gregminc/8-bit-CPU/Schematics/alu copy.kicad_sch

## KiCad design Schematics/alu copy.kicad_sch (2026-07-09)

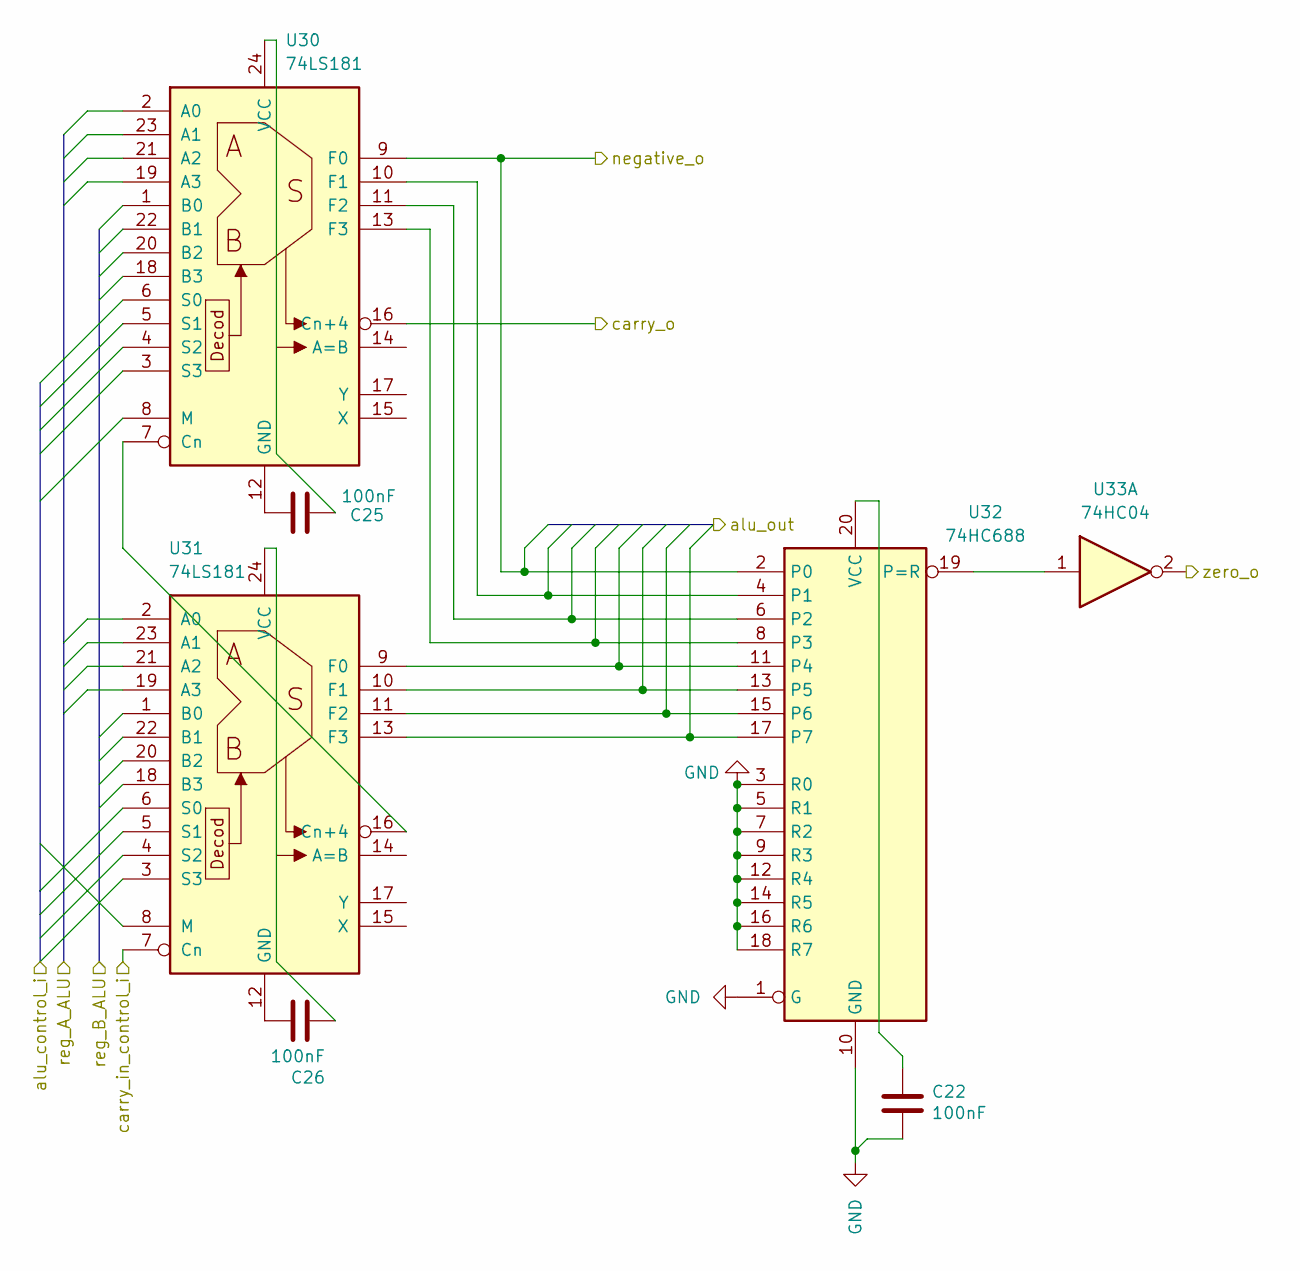
[picture p2: schematic alu copy.kicad_sch]

Parts:
C22, C25, C26: 100nF
U30, U31: 74LS181
U32: 74HC688
U33: 74HC04

Connections:
GND: C22.2, U32.1 (G), U32.3 (R0), U32.5 (R1), U32.7 (R2), U32.9 (R3), U32.10 (GND), U32.12 (R4), U32.14 (R5), U32.16 (R6), U32.18 (R7)
unnamed: C22.1, U32.20 (VCC)
unnamed: C25.1, U30.12 (GND)
unnamed: C25.2, U30.24 (VCC)
unnamed: C26.1, U31.12 (GND)
unnamed: C26.2, U31.24 (VCC)
unnamed: U30.7 (Cn), U31.16 (Cn+4)
unnamed: U30.10 (F1), U32.4 (P1)
unnamed: U30.11 (F2), U32.6 (P2)
unnamed: U30.13 (F3), U32.8 (P3)
unnamed: U31.6 (S0), U31.8 (M)
unnamed: U31.9 (F0), U32.11 (P4)
unnamed: U31.10 (F1), U32.13 (P5)
unnamed: U31.11 (F2), U32.15 (P6)
unnamed: U31.13 (F3), U32.17 (P7)
unnamed: U32.19 (P=R), U33.1
carry_in_control_i: U31.7 (Cn)
carry_o: U30.16 (Cn+4)
negative_o: U30.9 (F0), U32.2 (P0)
zero_o: U33.2
