gregminc/8-bit-CPU/Schematics/clock copy.kicad_sch

## KiCad design Schematics/clock copy.kicad_sch (2026-07-09)

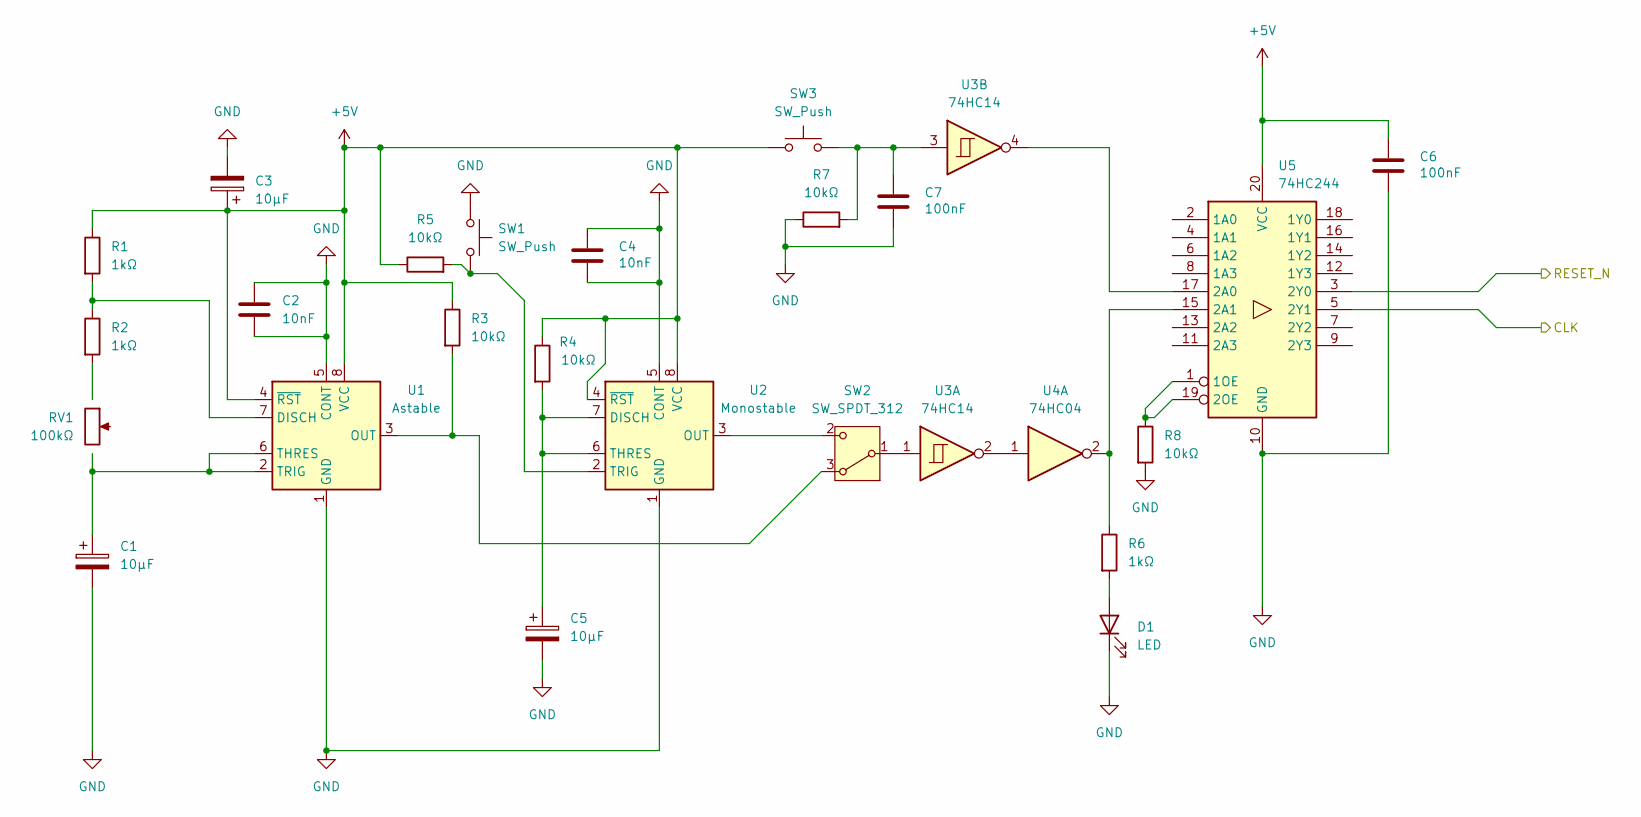
[picture p3: schematic clock copy.kicad_sch]

Parts:
C1, C3, C5: 10µF
C2, C4: 10nF
C6, C7: 100nF
D1: LED
R1, R2, R6: 1kΩ
R3, R4, R5, R7, R8: 10kΩ
RV1: 100kΩ
SW1, SW3: SW_Push
SW2: SW_SPDT_312
U1: Astable; DIP-8_W7.62mm
U2: Monostable; DIP-8_W7.62mm
U3: 74HC14
U4: 74HC04
U5: 74HC244

Connections:
+5V: C3.1, C6.1, R1.1, R3.1, R4.1, R5.1, SW3.1, U1.4 (~RST), U1.8 (VCC), U2.4 (~RST), U2.8 (VCC), U5.20 (VCC)
CLK: U5.5 (2Y1)
GND: C1.2, C2.1, C2.2, C3.2, C4.1, C4.2, C5.2, C6.2, C7.2, D1.1 (K), R7.1, R8.2, SW1.1, U1.1 (GND), U1.5 (CONT), U2.1 (GND), U2.5 (CONT), U5.10 (GND)
unnamed: C1.1, RV1.3, U1.2 (TRIG), U1.6 (THRES)
unnamed: C5.1, R4.2, U2.6 (THRES), U2.7 (DISCH)
unnamed: C7.1, R7.2, SW3.2, U3.3
unnamed: D1.2 (A), R6.2
unnamed: R1.2, R2.1, U1.7 (DISCH)
unnamed: R2.2, RV1.1
unnamed: R3.2, SW2.3 (A), U1.3 (OUT)
unnamed: R5.2, SW1.2, U2.2 (TRIG)
unnamed: R6.1, U4.2, U5.15 (2A1)
unnamed: R8.1, U5.1 (1OE), U5.19 (2OE)
unnamed: SW2.1 (B), U3.1
unnamed: SW2.2 (C), U2.3 (OUT)
unnamed: U3.2, U4.1
unnamed: U3.4, U5.17 (2A0)
RESET_N: U5.3 (2Y0)
