gregminc/8-bit-CPU/Schematics/cu copy.kicad_sch

## KiCad design Schematics/cu copy.kicad_sch (2026-07-09)

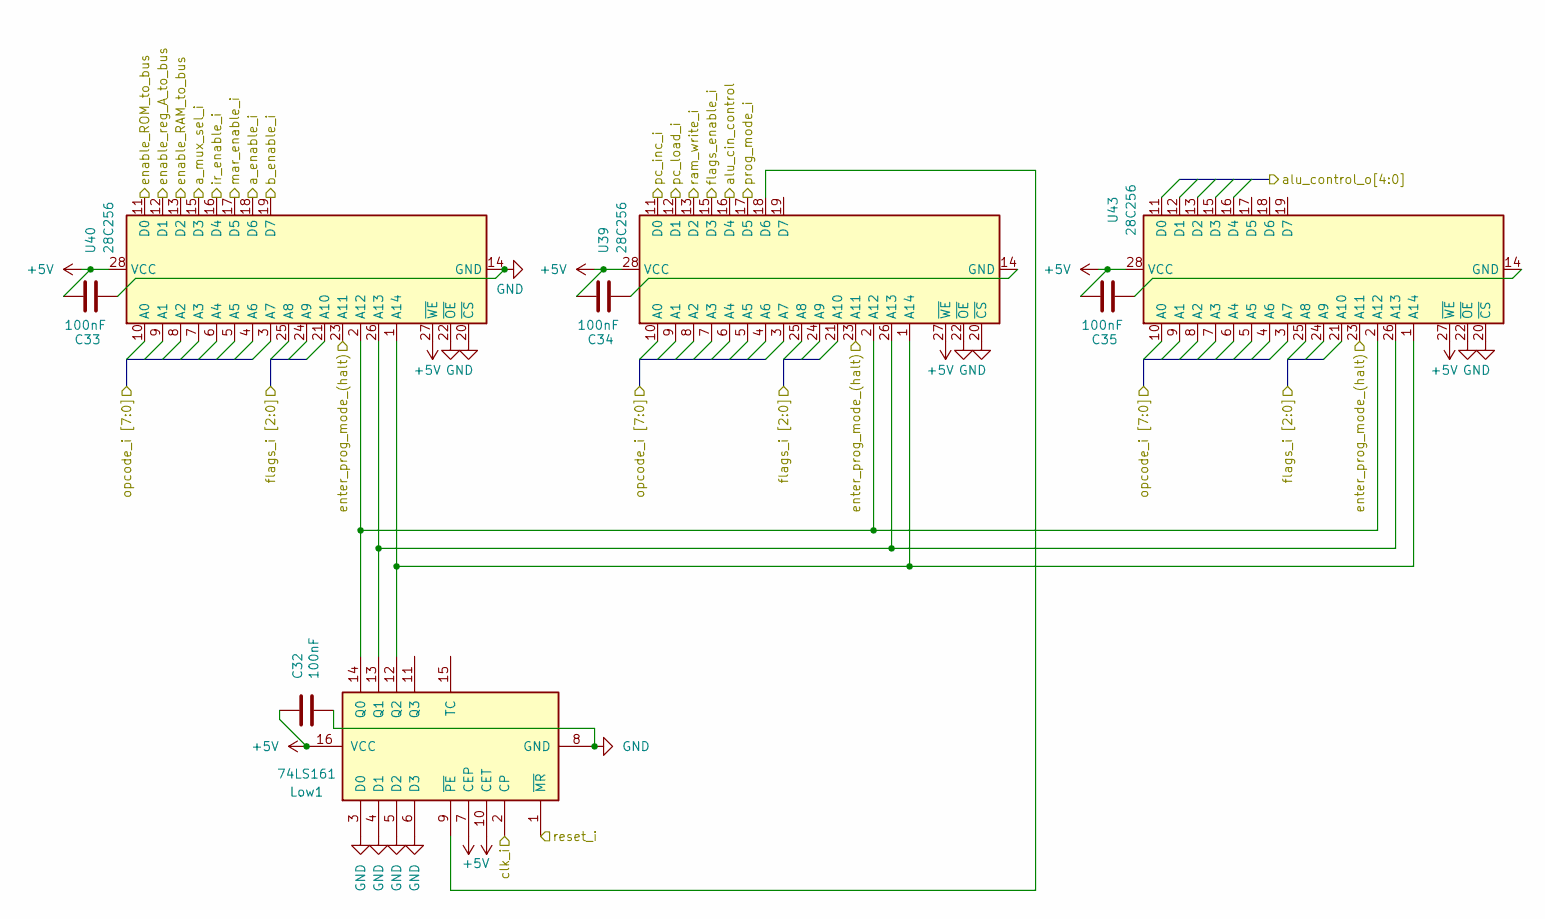
[picture p4: schematic cu copy.kicad_sch]

Parts:
C32, C33, C34, C35: 100nF
Low1: 74LS161
U39, U40, U43: 28C256

Connections:
+5V: C32.1, C33.1, C34.1, C35.1, Low1.7 (CEP), Low1.10 (CET), Low1.16 (VCC), U39.27 (~WE), U39.28 (VCC), U40.27 (~WE), U40.28 (VCC), U43.27 (~WE), U43.28 (VCC)
GND: C32.2, C33.2, Low1.3 (D0), Low1.4 (D1), Low1.5 (D2), Low1.6 (D3), Low1.8 (GND), U39.20 (~CS), U39.22 (~OE), U40.14 (GND), U40.20 (~CS), U40.22 (~OE), U43.20 (~CS), U43.22 (~OE)
unnamed: C34.2, U39.14 (GND)
unnamed: C35.2, U43.14 (GND)
unnamed: Low1.9 (~PE), U39.18 (D6)
unnamed: Low1.12 (Q2), U39.1 (A14), U40.1 (A14), U43.1 (A14)
unnamed: Low1.13 (Q1), U39.26 (A13), U40.26 (A13), U43.26 (A13)
unnamed: Low1.14 (Q0), U39.2 (A12), U40.2 (A12), U43.2 (A12)
a_enable_i: U40.18 (D6)
a_mux_sel_i: U40.15 (D3)
alu_cin_control: U39.16 (D4)
b_enable_i: U40.19 (D7)
clk_i: Low1.2 (CP)
enable_RAM_to_bus: U40.13 (D2)
enable_ROM_to_bus: U40.11 (D0)
enable_reg_A_to_bus: U40.12 (D1)
enter_prog_mode_(halt): U39.23 (A11), U40.23 (A11), U43.23 (A11)
flags_enable_i: U39.15 (D3)
ir_enable_i: U40.16 (D4)
mar_enable_i: U40.17 (D5)
pc_inc_i: U39.11 (D0)
pc_load_i: U39.12 (D1)
prog_mode_i: U39.17 (D5)
ram_write_i: U39.13 (D2)
reset_i: Low1.1 (~MR)
