gregminc/8-bit-CPU/Schematics/flags copy.kicad_sch

## KiCad design Schematics/flags copy.kicad_sch (2026-07-09)

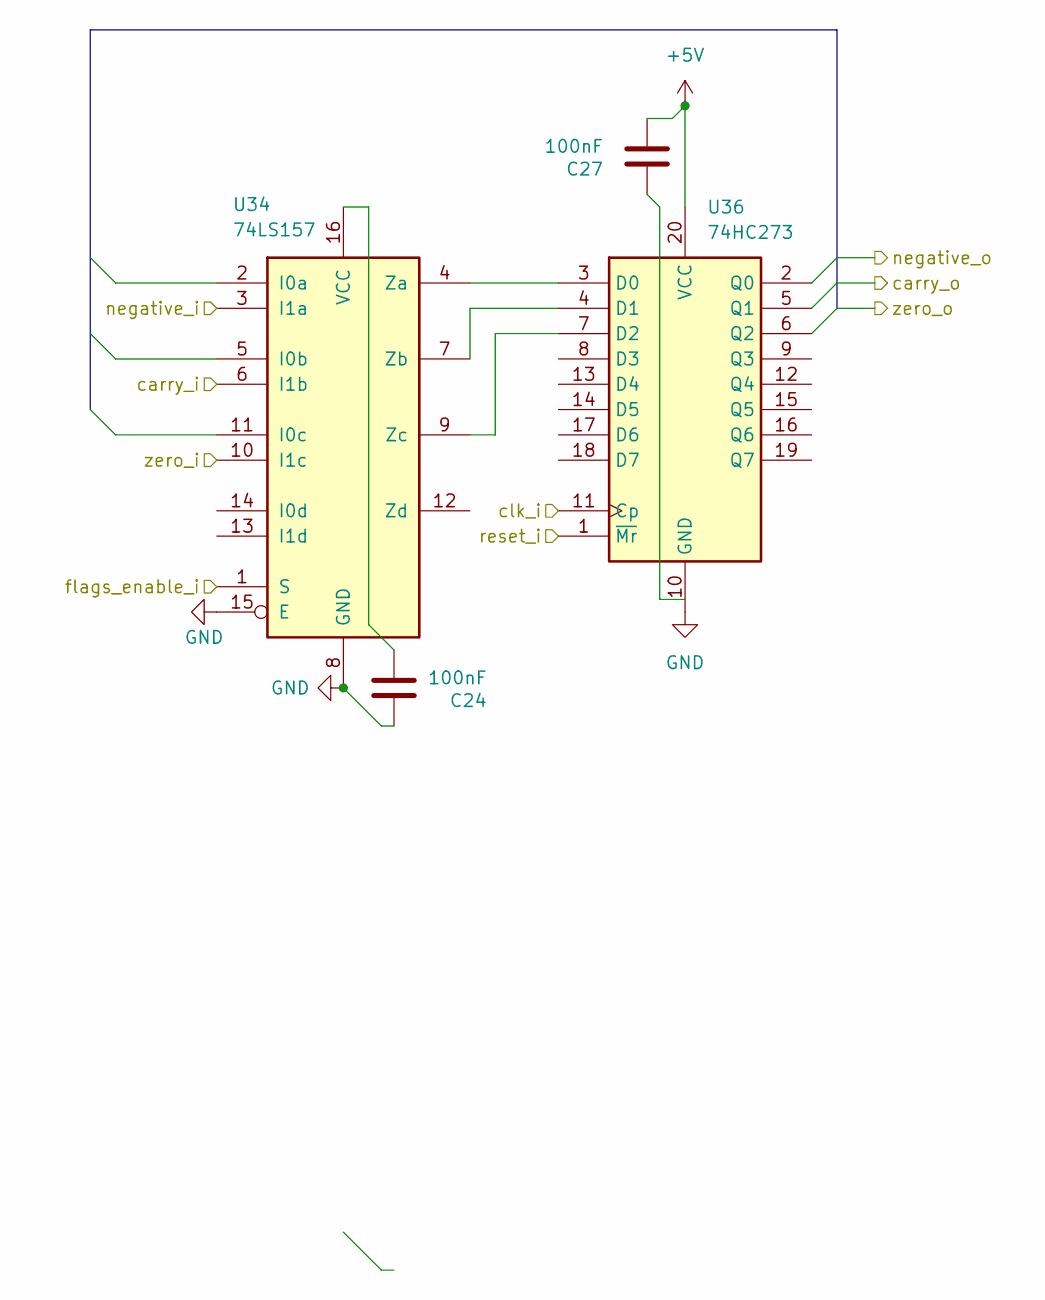
[picture p5: schematic flags copy.kicad_sch]

Parts:
C24, C27: 100nF
U34: 74LS157
U36: 74HC273

Connections:
+5V: C27.2, U36.20 (VCC)
GND: C24.1, U34.8 (GND), U34.15 (E), U36.10 (GND)
unnamed: C24.2, U34.16 (VCC)
unnamed: U34.4 (Za), U36.3 (D0)
unnamed: U34.7 (Zb), U36.4 (D1)
unnamed: U34.9 (Zc), U36.7 (D2)
carry_i: U34.6 (I1b)
clk_i: U36.11 (Cp)
flags_enable_i: U34.1 (S)
negative_i: U34.3 (I1a)
reset_i: U36.1 (~Mr)
zero_i: U34.10 (I1c)
