gregminc/8-bit-CPU/Schematics/io copy.kicad_sch

## KiCad design Schematics/io copy.kicad_sch (2026-07-09)

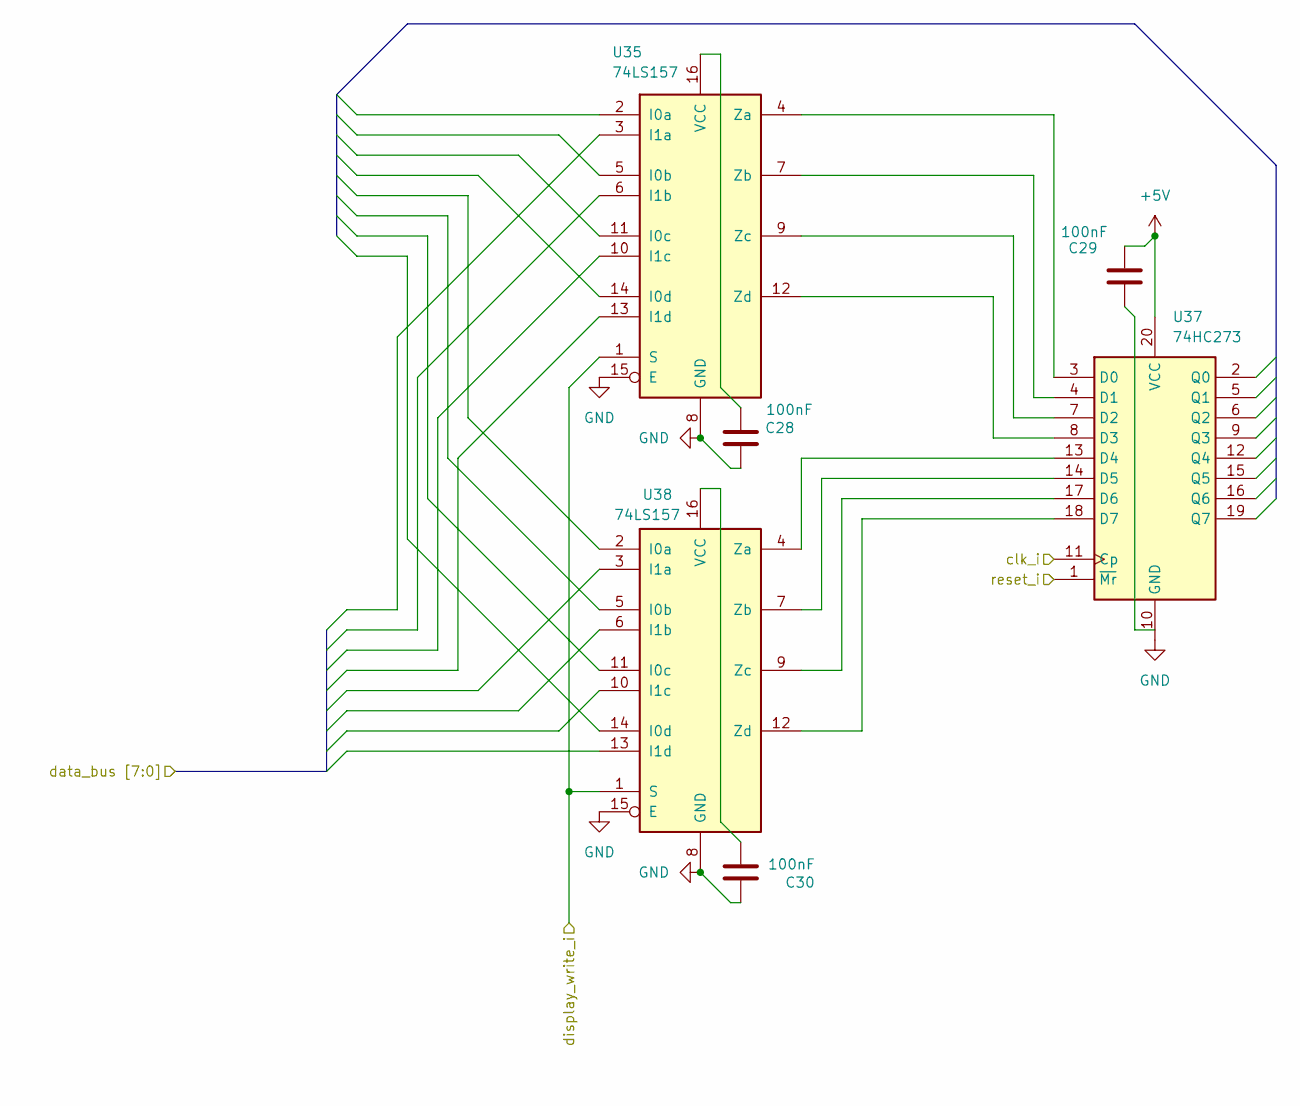
[picture p6: schematic io copy.kicad_sch]

Parts:
C28, C29, C30: 100nF
U35, U38: 74LS157
U37: 74HC273

Connections:
+5V: C29.2, U37.20 (VCC)
GND: C28.1, C30.1, U35.8 (GND), U35.15 (E), U37.10 (GND), U38.8 (GND), U38.15 (E)
unnamed: C28.2, U35.16 (VCC)
unnamed: C30.2, U38.16 (VCC)
unnamed: U35.4 (Za), U37.3 (D0)
unnamed: U35.7 (Zb), U37.4 (D1)
unnamed: U35.9 (Zc), U37.7 (D2)
unnamed: U35.12 (Zd), U37.8 (D3)
unnamed: U37.13 (D4), U38.4 (Za)
unnamed: U37.14 (D5), U38.7 (Zb)
unnamed: U37.17 (D6), U38.9 (Zc)
unnamed: U37.18 (D7), U38.12 (Zd)
clk_i: U37.11 (Cp)
display_write_i: U35.1 (S), U38.1 (S)
reset_i: U37.1 (~Mr)
