gregminc/8-bit-CPU/Schematics/ir copy.kicad_sch

## KiCad design Schematics/ir copy.kicad_sch (2026-07-09)

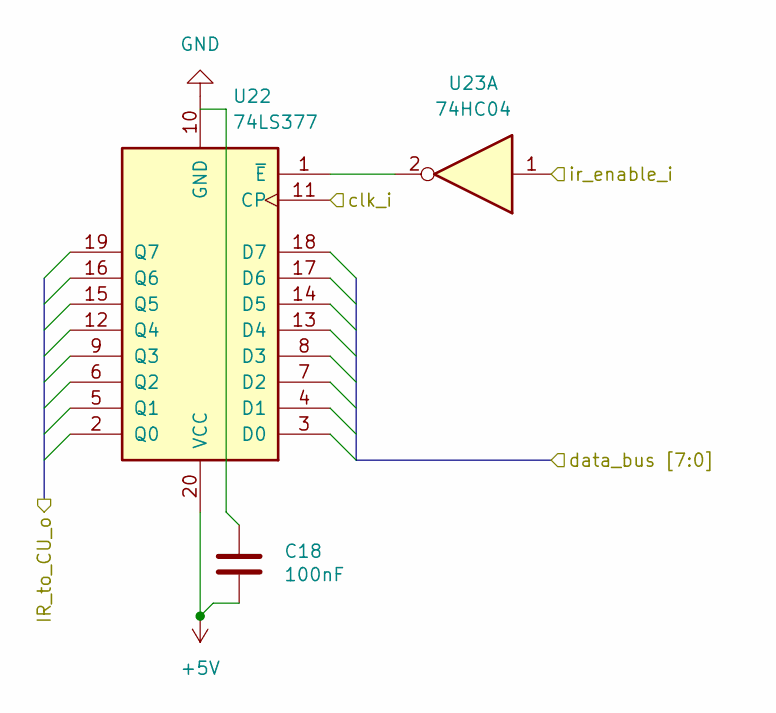
[picture p7: schematic ir copy.kicad_sch]

Parts:
C18: 100nF
U22: 74LS377
U23: 74HC04

Connections:
+5V: C18.2, U22.20 (VCC)
GND: U22.10 (GND)
unnamed: U22.1 (~E), U23.2
clk_i: U22.11 (CP)
ir_enable_i: U23.1
