gregminc/8-bit-CPU/Schematics/mar copy.kicad_sch

## KiCad design Schematics/mar copy.kicad_sch (2026-07-09)

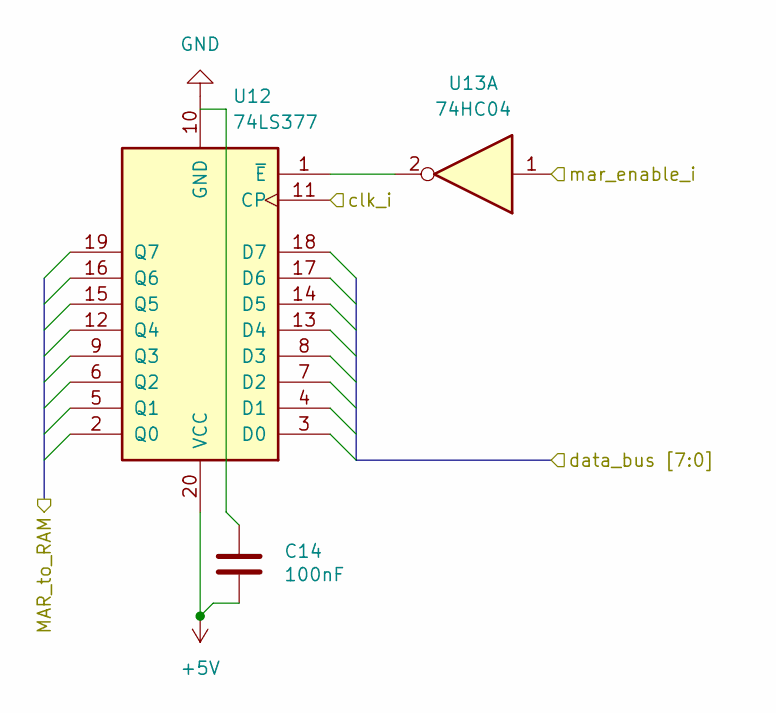
[picture p8: schematic mar copy.kicad_sch]

Parts:
C14: 100nF
U12: 74LS377
U13: 74HC04

Connections:
+5V: C14.2, U12.20 (VCC)
GND: U12.10 (GND)
unnamed: U12.1 (~E), U13.2
clk_i: U12.11 (CP)
mar_enable_i: U13.1
