gregminc/8-bit-CPU/Schematics/pc copy.kicad_sch

## KiCad design Schematics/pc copy.kicad_sch (2026-07-09)

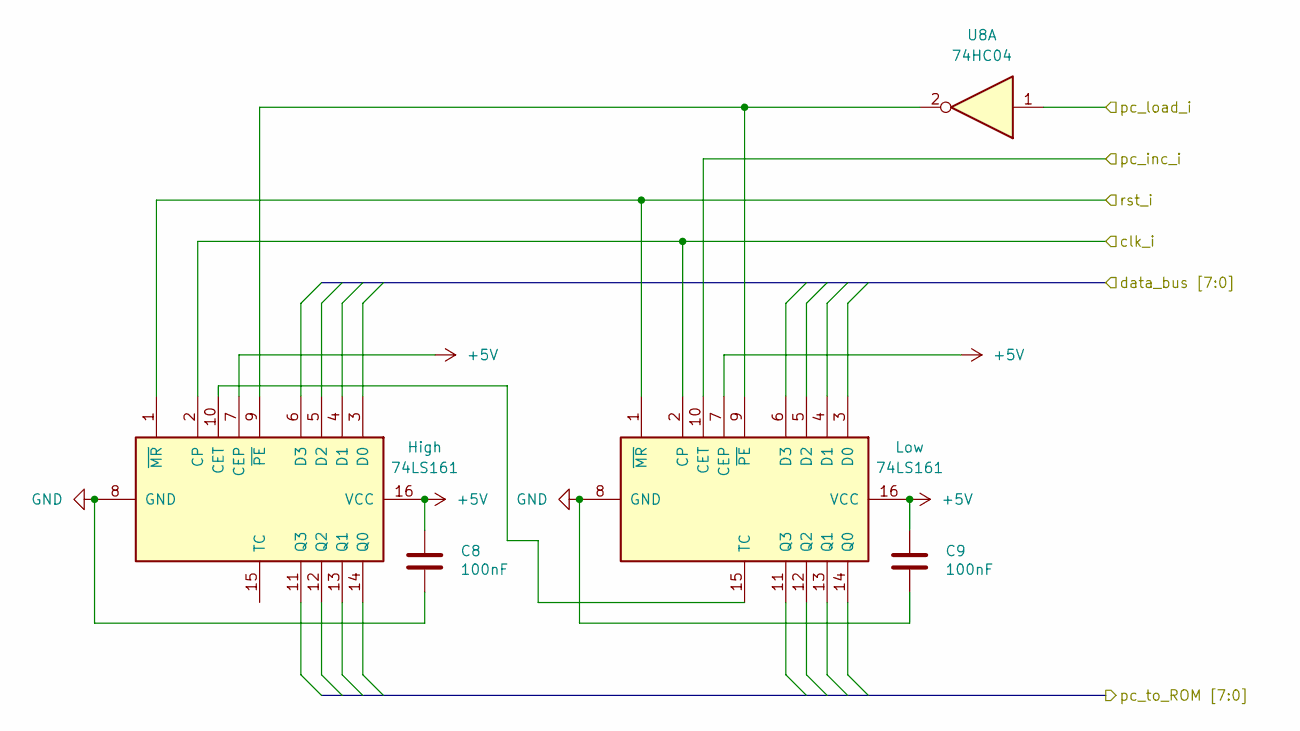
[picture p9: schematic pc copy.kicad_sch]

Parts:
C8, C9: 100nF
High: 74LS161
Low: 74LS161
U8: 74HC04

Connections:
+5V: C8.1, C9.1, High.7 (CEP), High.16 (VCC), Low.7 (CEP), Low.16 (VCC)
GND: C8.2, C9.2, High.8 (GND), Low.8 (GND)
unnamed: High.9 (~PE), Low.9 (~PE), U8.2
unnamed: High.10 (CET), Low.15 (TC)
clk_i: High.2 (CP), Low.2 (CP)
pc_inc_i: Low.10 (CET)
pc_load_i: U8.1
rst_i: High.1 (~MR), Low.1 (~MR)
