gregminc/8-bit-CPU/Schematics/ram copy.kicad_sch

## KiCad design Schematics/ram copy.kicad_sch (2026-07-09)

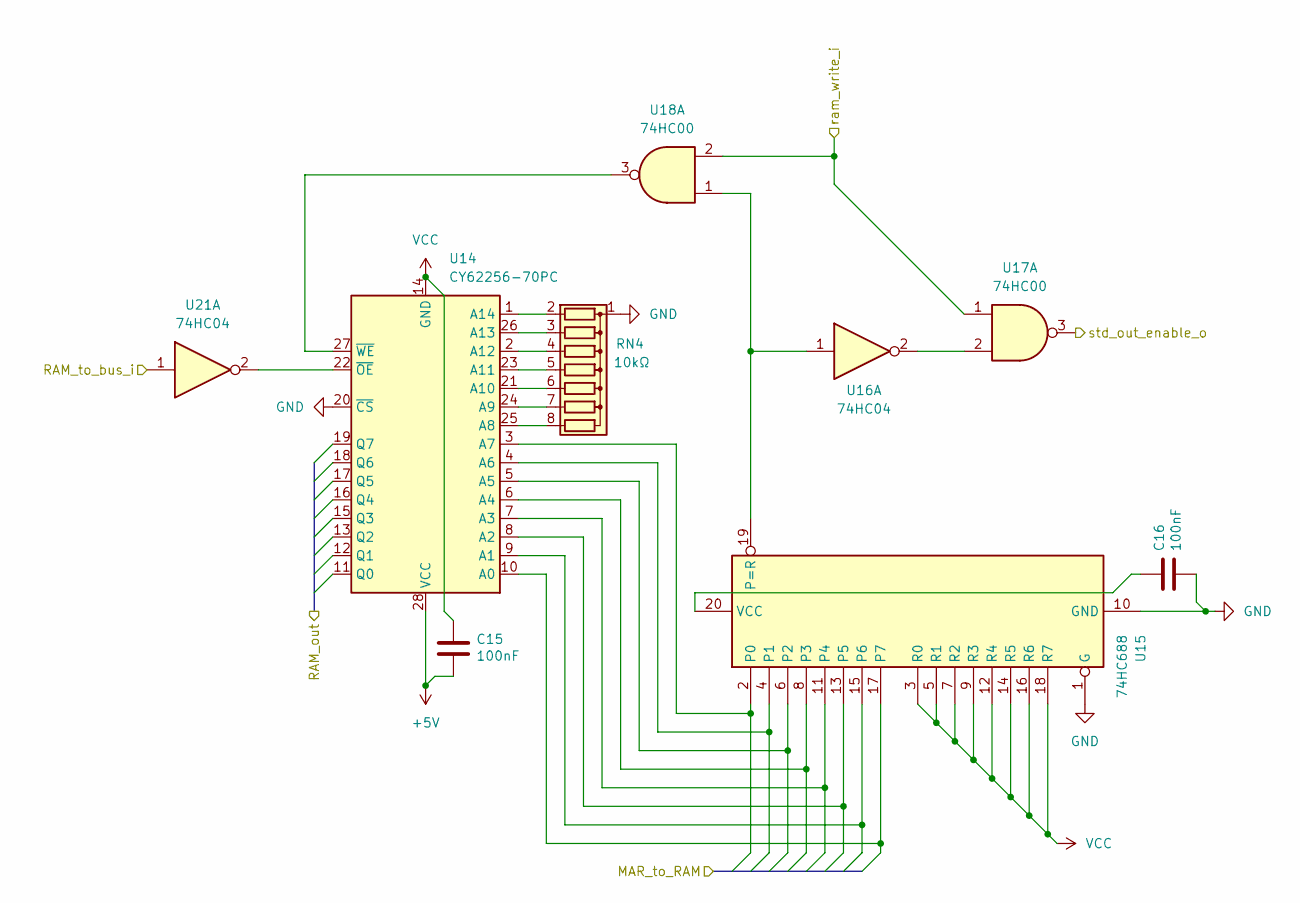
[picture p10: schematic ram copy.kicad_sch]

Parts:
C15, C16: 100nF
RN4: 10kΩ; R_Array_SIP8
U14: CY62256-70PC; DIP-28_W15.24mm
U15: 74HC688
U16, U21: 74HC04
U17, U18: 74HC00

Connections:
+5V: C15.2, U14.28 (VCC)
GND: C16.2, RN4.1 (common), U14.20 (~CS), U15.1 (G), U15.10 (GND)
unnamed: C16.1, U15.20 (VCC)
unnamed: RN4.2 (R1), U14.1 (A14)
unnamed: RN4.3 (R2), U14.26 (A13)
unnamed: RN4.4 (R3), U14.2 (A12)
unnamed: RN4.5 (R4), U14.23 (A11)
unnamed: RN4.6 (R5), U14.21 (A10)
unnamed: RN4.7 (R6), U14.24 (A9)
unnamed: RN4.8 (R7), U14.25 (A8)
unnamed: U14.3 (A7), U15.2 (P0)
unnamed: U14.4 (A6), U15.4 (P1)
unnamed: U14.5 (A5), U15.6 (P2)
unnamed: U14.6 (A4), U15.8 (P3)
unnamed: U14.7 (A3), U15.11 (P4)
unnamed: U14.8 (A2), U15.13 (P5)
unnamed: U14.9 (A1), U15.15 (P6)
unnamed: U14.10 (A0), U15.17 (P7)
unnamed: U14.22 (~OE), U21.2
unnamed: U14.27 (~WE), U18.3
unnamed: U15.19 (P=R), U16.1, U18.1
unnamed: U16.2, U17.2
RAM_to_bus_i: U21.1
VCC: C15.1, U14.14 (GND), U15.3 (R0), U15.5 (R1), U15.7 (R2), U15.9 (R3), U15.12 (R4), U15.14 (R5), U15.16 (R6), U15.18 (R7)
ram_write_i: U17.1, U18.2
std_out_enable_o: U17.3
