gregminc/8-bit-CPU/Schematics/reg_a copy.kicad_sch

## KiCad design Schematics/reg_a copy.kicad_sch (2026-07-09)

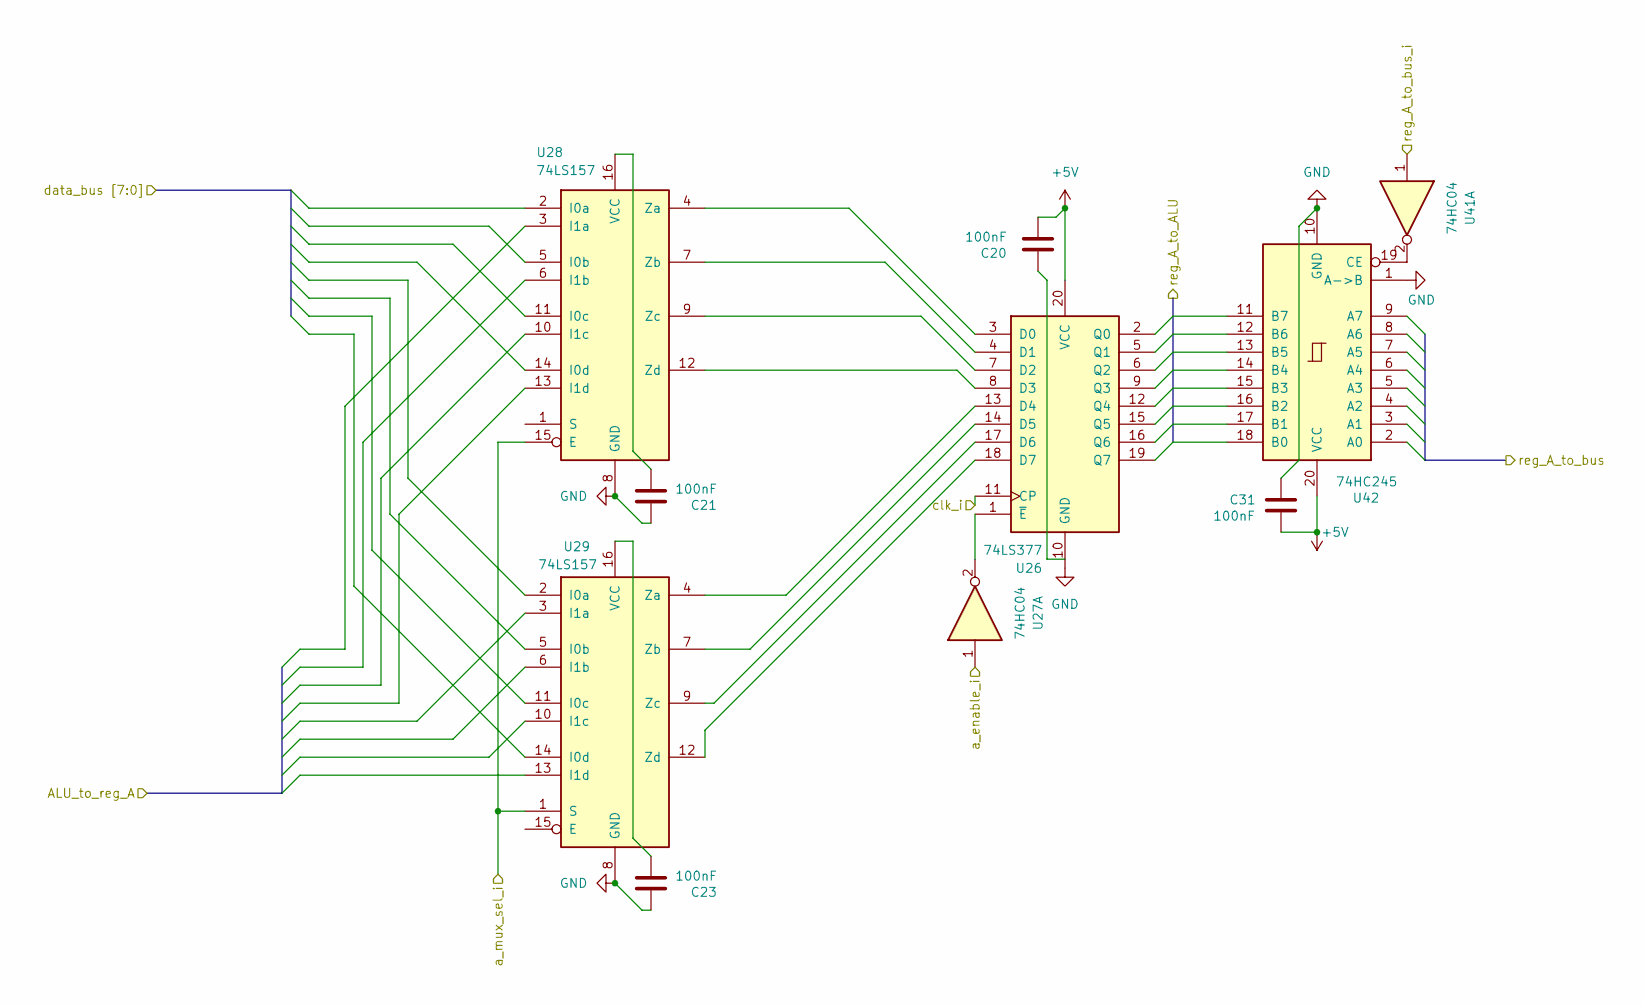
[picture p11: schematic reg_a copy.kicad_sch]

Parts:
C20, C21, C23, C31: 100nF
U26: 74LS377
U27, U41: 74HC04
U28, U29: 74LS157
U42: 74HC245

Connections:
+5V: C20.2, C31.2, U26.20 (VCC), U42.20 (VCC)
GND: C21.1, C23.1, C31.1, U26.10 (GND), U28.8 (GND), U29.8 (GND), U42.1 (A->B), U42.10 (GND)
unnamed: C21.2, U28.16 (VCC)
unnamed: C23.2, U29.16 (VCC)
unnamed: U26.1 (~E), U27.2
unnamed: U26.3 (D0), U28.4 (Za)
unnamed: U26.4 (D1), U28.7 (Zb)
unnamed: U26.7 (D2), U28.9 (Zc)
unnamed: U26.8 (D3), U28.12 (Zd)
unnamed: U26.13 (D4), U29.4 (Za)
unnamed: U26.14 (D5), U29.7 (Zb)
unnamed: U26.17 (D6), U29.9 (Zc)
unnamed: U26.18 (D7), U29.12 (Zd)
unnamed: U41.2, U42.19 (CE)
a_enable_i: U27.1
a_mux_sel_i: U28.15 (E), U29.1 (S)
clk_i: U26.11 (CP)
reg_A_to_bus_i: U41.1
