gregminc/8-bit-CPU/Schematics/register_b copy.kicad_sch

## KiCad design Schematics/register_b copy.kicad_sch (2026-07-09)

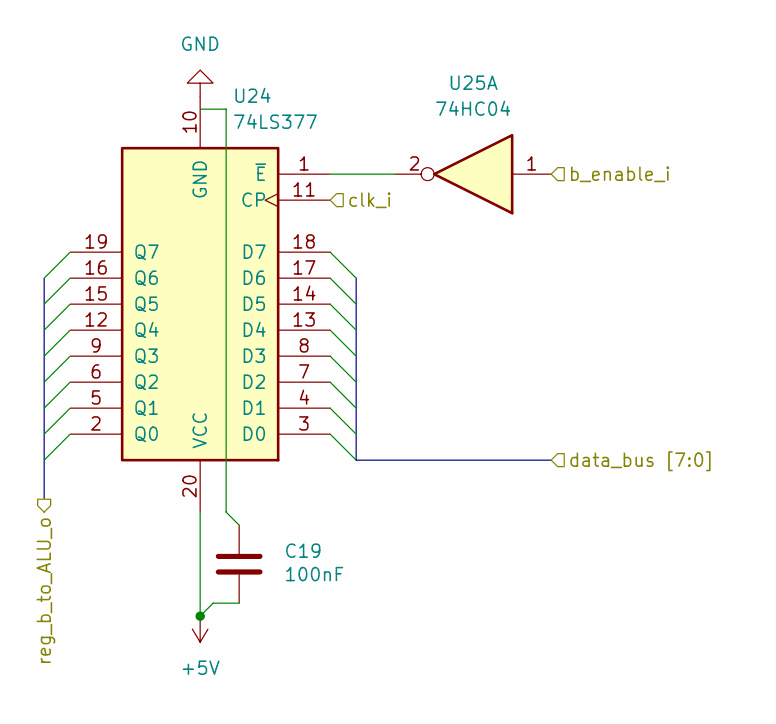
[picture p12: schematic register_b copy.kicad_sch]

Parts:
C19: 100nF
U24: 74LS377
U25: 74HC04

Connections:
+5V: C19.2, U24.20 (VCC)
GND: U24.10 (GND)
unnamed: U24.1 (~E), U25.2
b_enable_i: U25.1
clk_i: U24.11 (CP)
