gregminc/8-bit-CPU/Schematics/rom copy.kicad_sch

## KiCad design Schematics/rom copy.kicad_sch (2026-07-09)

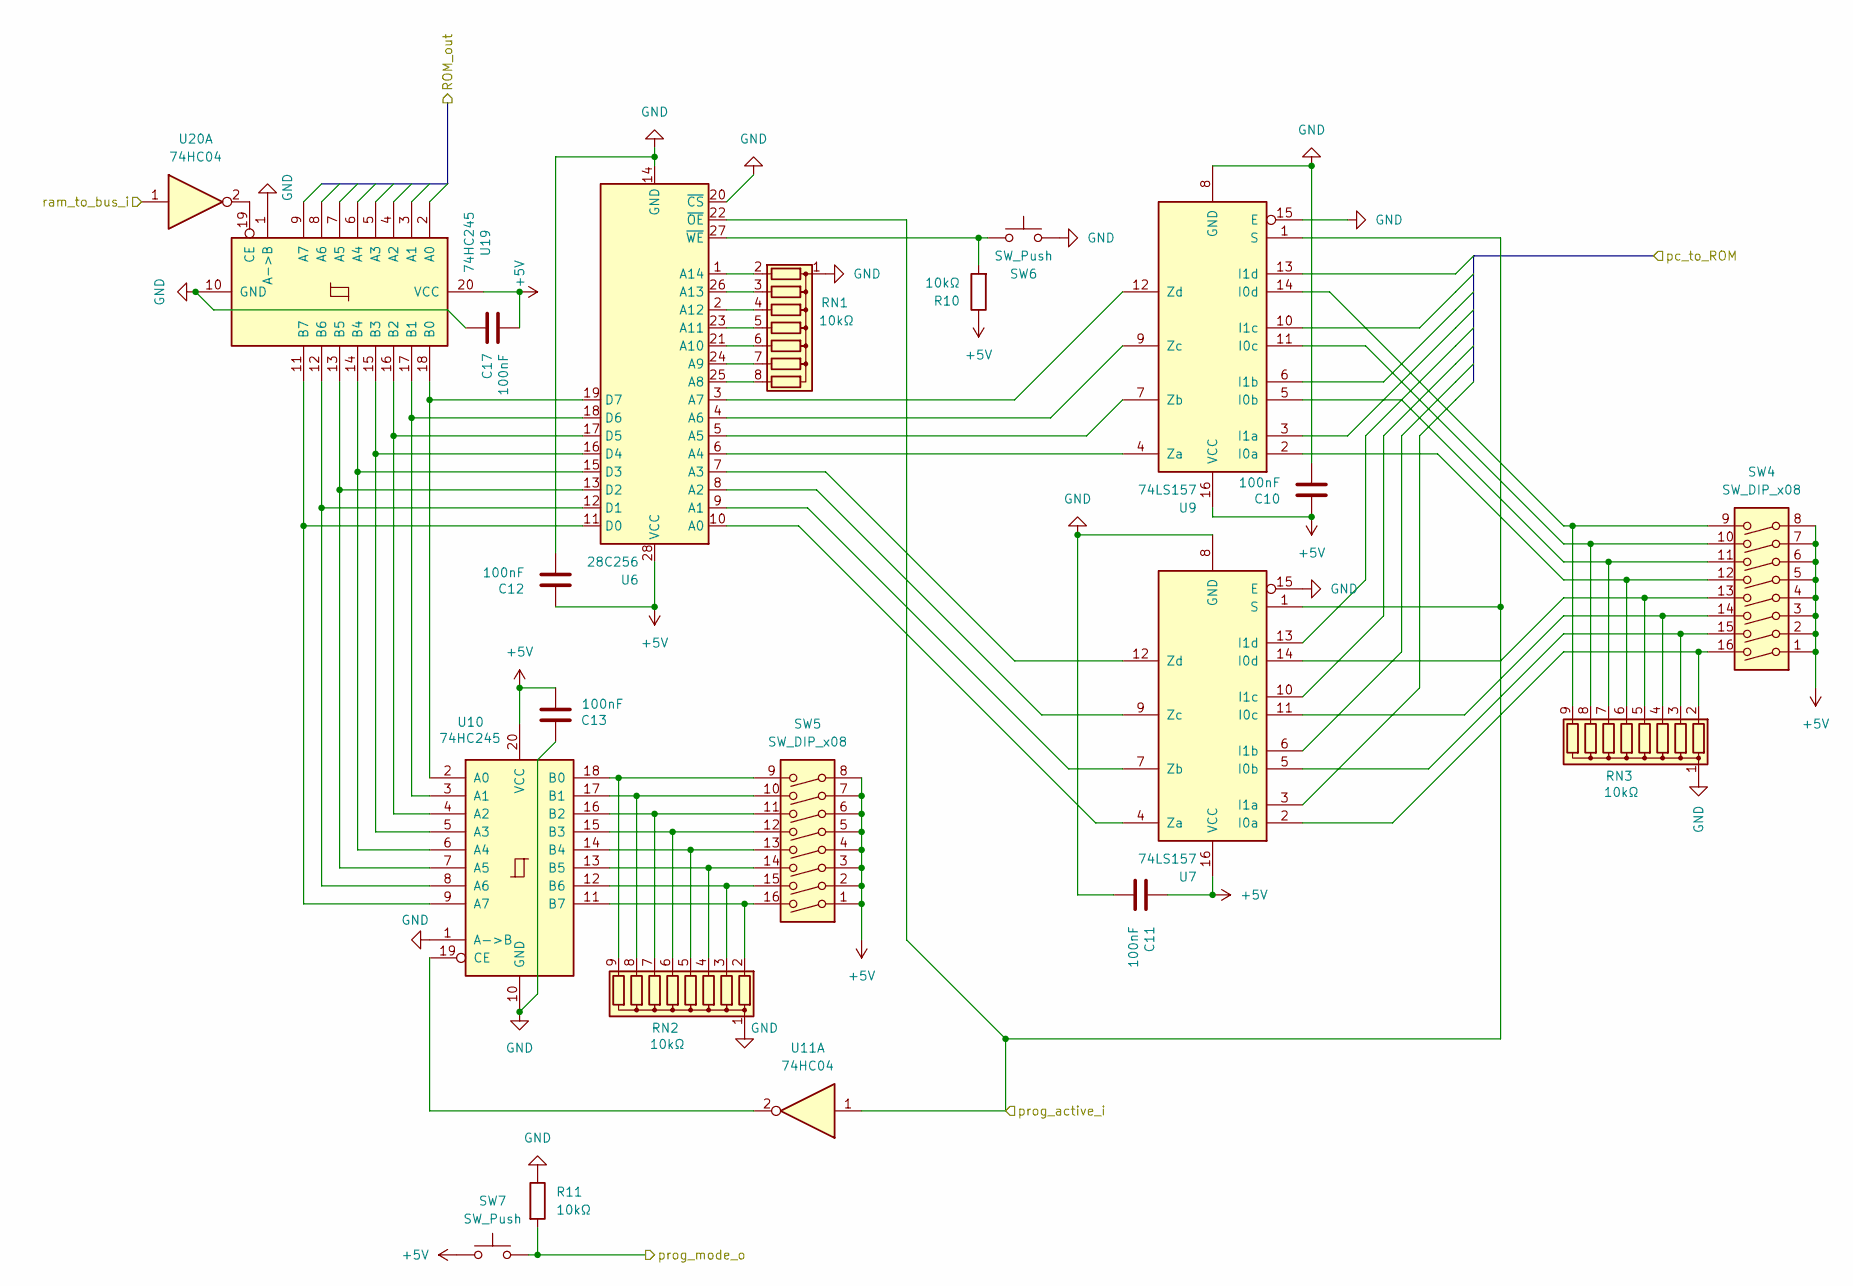
[picture p13: schematic rom copy.kicad_sch]

Parts:
C10, C11, C12, C13, C17: 100nF
R10, R11: 10kΩ
RN1: 10kΩ; R_Array_SIP8
RN2, RN3: 10kΩ; R_Array_SIP9
SW4, SW5: SW_DIP_x08
SW6, SW7: SW_Push
U6: 28C256
U7, U9: 74LS157
U10, U19: 74HC245
U11, U20: 74HC04

Connections:
+5V: C10.1, C11.1, C12.1, C13.2, C17.2, R10.1, SW4.1, SW4.2, SW4.3, SW4.4, SW4.5, SW4.6, SW4.7, SW4.8, SW5.1, SW5.2, SW5.3, SW5.4, SW5.5, SW5.6, SW5.7, SW5.8, SW7.1, U6.28 (VCC), U7.16 (VCC), U9.16 (VCC), U10.20 (VCC), U19.20 (VCC)
GND: C10.2, C11.2, C12.2, C13.1, C17.1, R11.1, RN1.1 (common), RN2.1 (common), RN3.1 (common), SW6.2, U6.14 (GND), U6.20 (~CS), U7.8 (GND), U7.15 (E), U9.8 (GND), U9.15 (E), U10.1 (A->B), U10.10 (GND), U19.1 (A->B), U19.10 (GND)
unnamed: R10.2, SW6.1, U6.27 (~WE)
unnamed: RN1.2 (R1), U6.1 (A14)
unnamed: RN1.3 (R2), U6.26 (A13)
unnamed: RN1.4 (R3), U6.2 (A12)
unnamed: RN1.5 (R4), U6.23 (A11)
unnamed: RN1.6 (R5), U6.21 (A10)
unnamed: RN1.7 (R6), U6.24 (A9)
unnamed: RN1.8 (R7), U6.25 (A8)
unnamed: RN2.2 (R1), SW5.16, U10.11 (B7)
unnamed: RN2.3 (R2), SW5.15, U10.12 (B6)
unnamed: RN2.4 (R3), SW5.14, U10.13 (B5)
unnamed: RN2.5 (R4), SW5.13, U10.14 (B4)
unnamed: RN2.6 (R5), SW5.12, U10.15 (B3)
unnamed: RN2.7 (R6), SW5.11, U10.16 (B2)
unnamed: RN2.8 (R7), SW5.10, U10.17 (B1)
unnamed: RN2.9 (R8), SW5.9, U10.18 (B0)
unnamed: RN3.2 (R1), SW4.16, U7.2 (I0a)
unnamed: RN3.3 (R2), SW4.15, U7.5 (I0b)
unnamed: RN3.4 (R3), SW4.14, U7.11 (I0c)
unnamed: RN3.5 (R4), SW4.13, U7.14 (I0d)
unnamed: RN3.6 (R5), SW4.12, U9.2 (I0a)
unnamed: RN3.7 (R6), SW4.11, U9.5 (I0b)
unnamed: RN3.8 (R7), SW4.10, U9.11 (I0c)
unnamed: RN3.9 (R8), SW4.9, U9.14 (I0d)
unnamed: U6.3 (A7), U9.12 (Zd)
unnamed: U6.4 (A6), U9.9 (Zc)
unnamed: U6.5 (A5), U9.7 (Zb)
unnamed: U6.6 (A4), U9.4 (Za)
unnamed: U6.7 (A3), U7.12 (Zd)
unnamed: U6.8 (A2), U7.9 (Zc)
unnamed: U6.9 (A1), U7.7 (Zb)
unnamed: U6.10 (A0), U7.4 (Za)
unnamed: U6.19 (D7), U10.2 (A0), U19.18 (B0)
unnamed: U6.18 (D6), U10.3 (A1), U19.17 (B1)
unnamed: U6.17 (D5), U10.4 (A2), U19.16 (B2)
unnamed: U6.16 (D4), U10.5 (A3), U19.15 (B3)
unnamed: U6.15 (D3), U10.6 (A4), U19.14 (B4)
unnamed: U6.13 (D2), U10.7 (A5), U19.13 (B5)
unnamed: U6.12 (D1), U10.8 (A6), U19.12 (B6)
unnamed: U6.11 (D0), U10.9 (A7), U19.11 (B7)
unnamed: U10.19 (CE), U11.2
unnamed: U19.19 (CE), U20.2
prog_active_i: U6.22 (~OE), U7.1 (S), U9.1 (S), U11.1
prog_mode_o: R11.2, SW7.2
ram_to_bus_i: U20.1
